aditya23043/split_keyboard/electroholics/2024-12-25_12-39.png

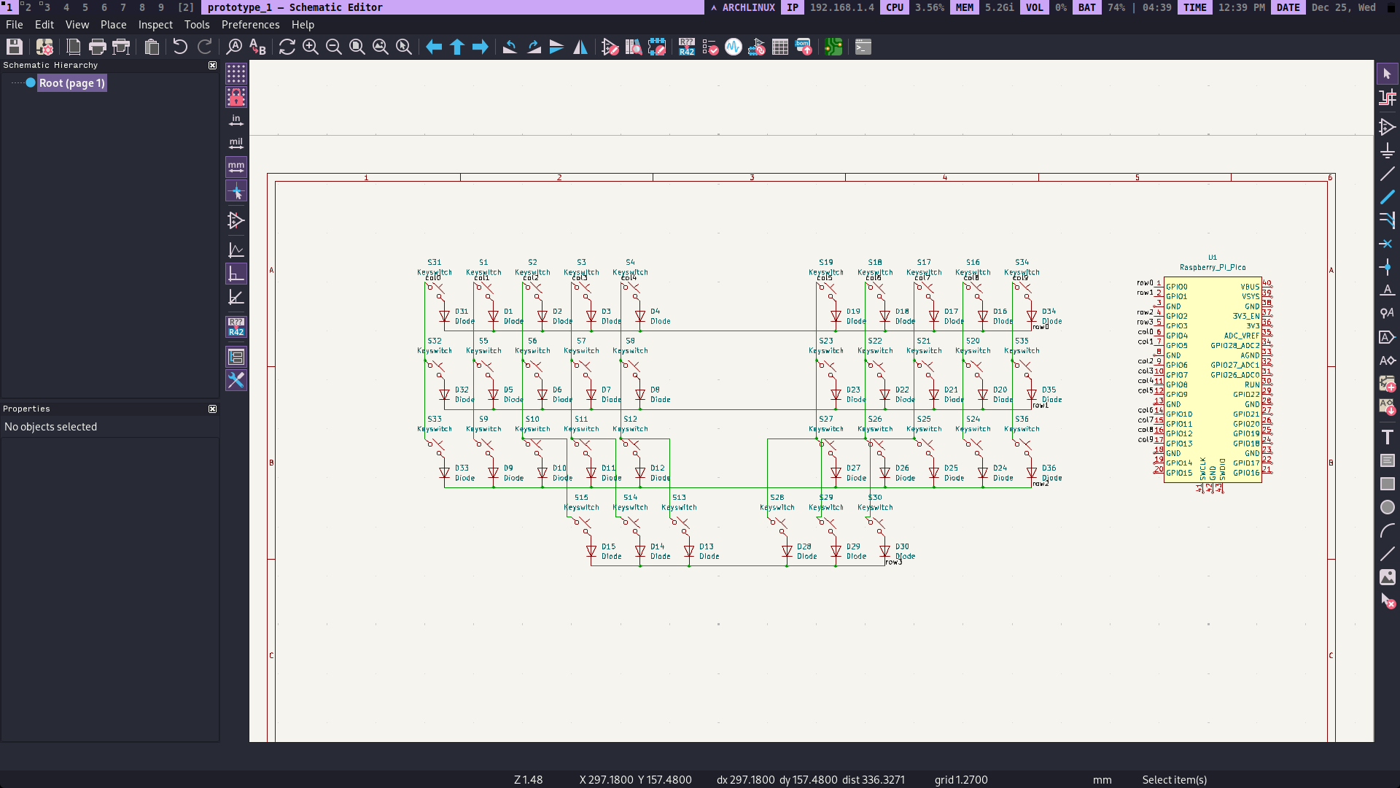
electroholics/2024-12-25_12-39.png
