aditya23043/split_keyboard/imgs/7.jpeg

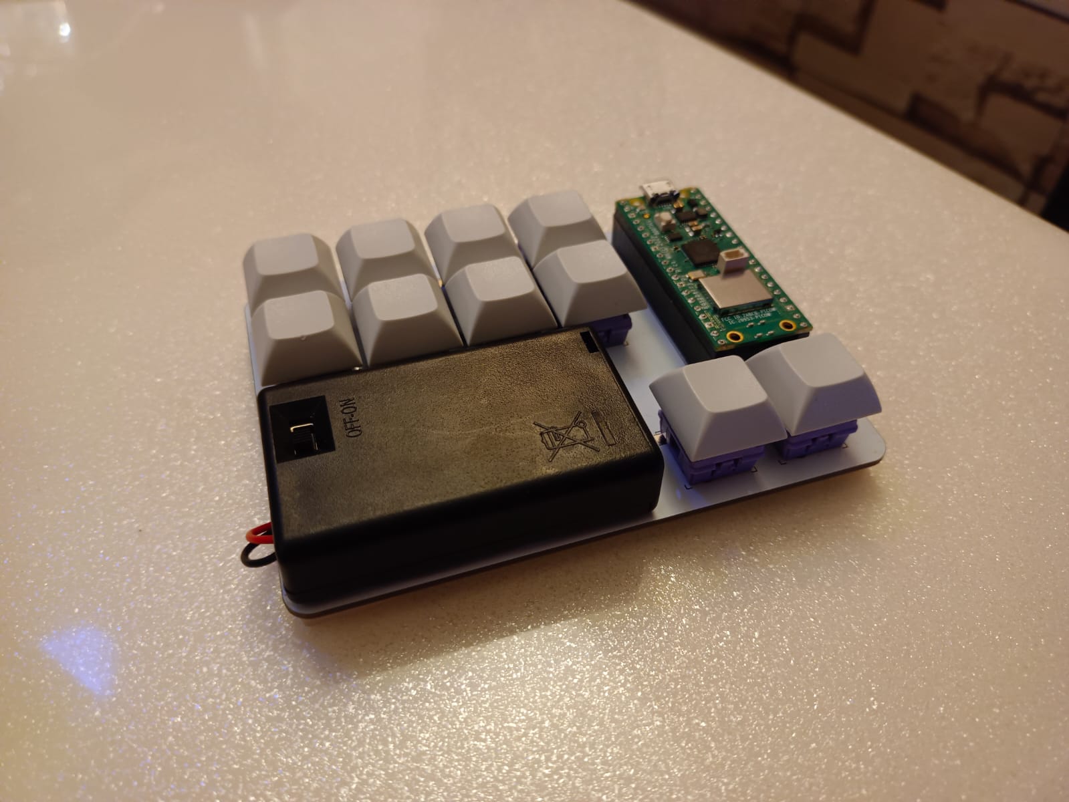
imgs/7.jpeg
