aditya23043/split_keyboard/imgs/8.jpeg

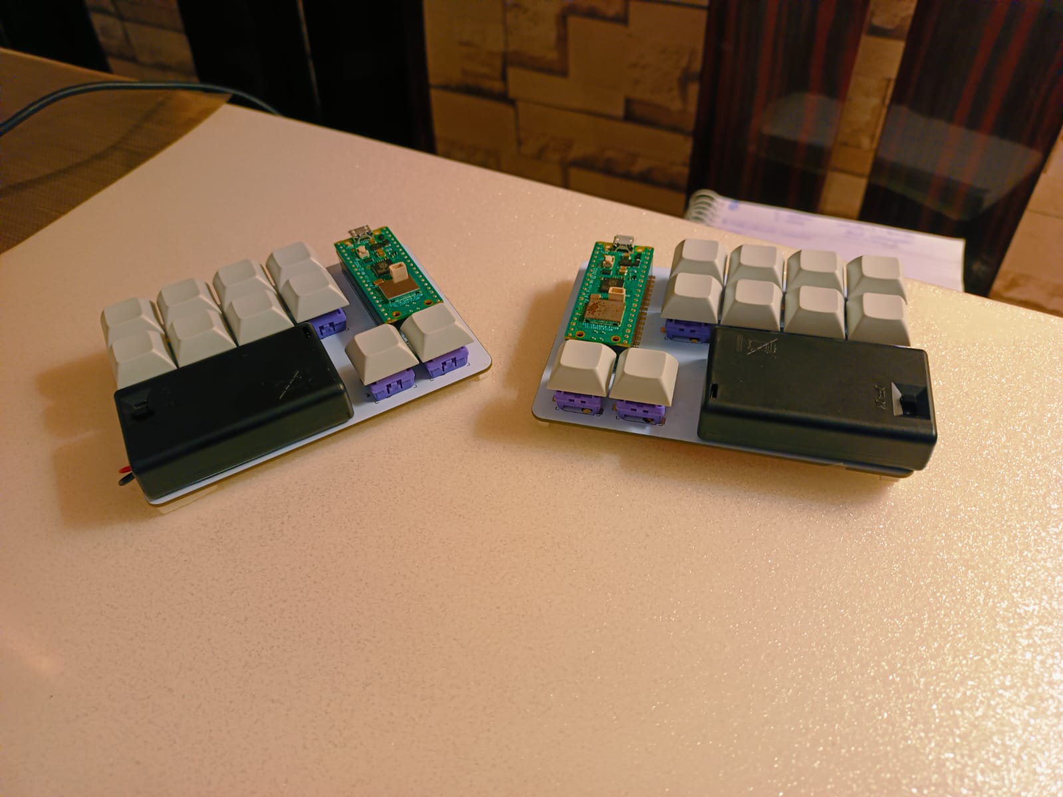
imgs/8.jpeg
