aditya23043/split_keyboard/imgs/10.jpeg

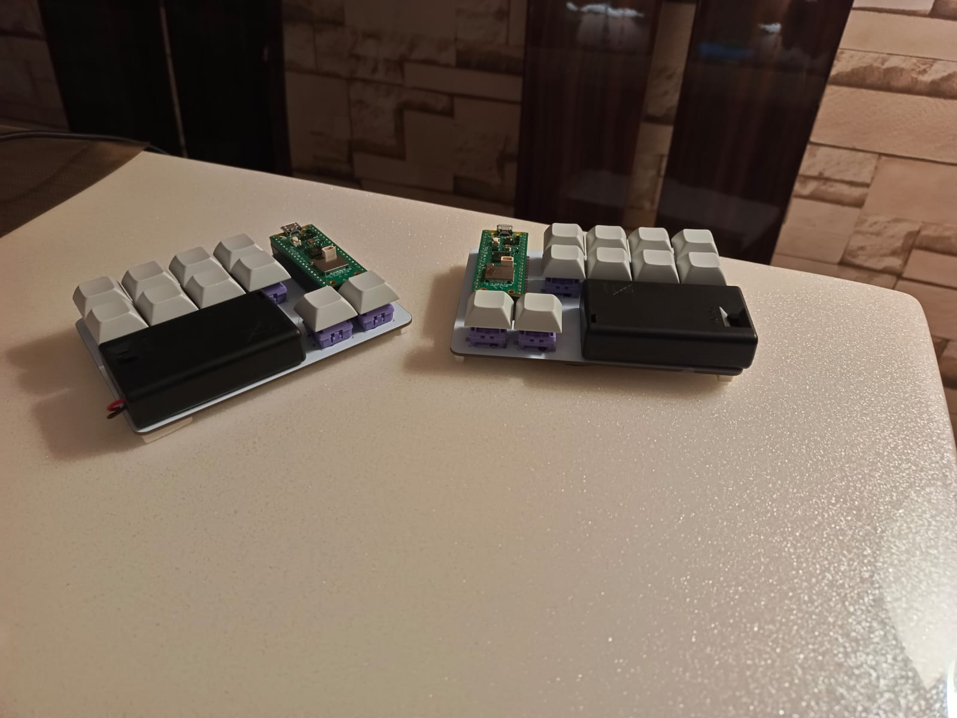
imgs/10.jpeg
