aditya23043/split_keyboard/imgs/13.jpeg

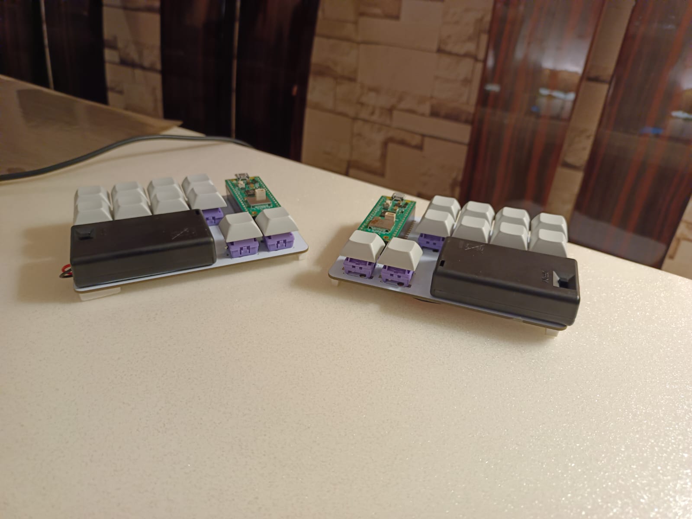
imgs/13.jpeg
