aditya23043/split_keyboard/imgs/22.jpeg

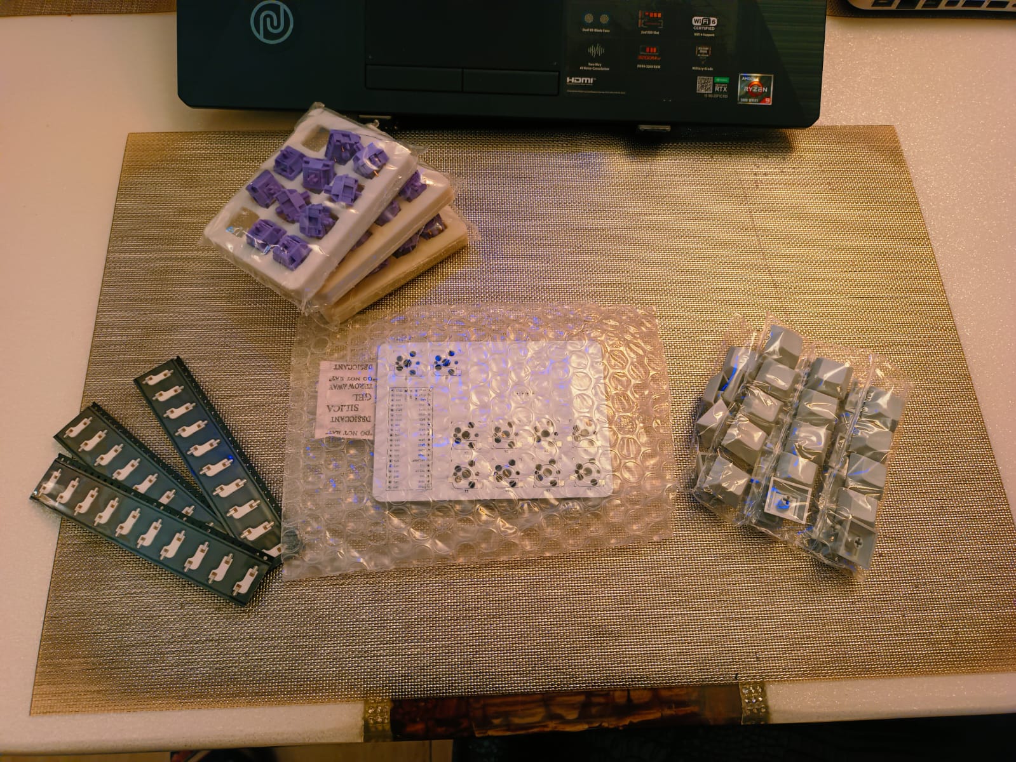
imgs/22.jpeg
