aditya23043/split_keyboard/imgs/2024-10-22_10-09.png

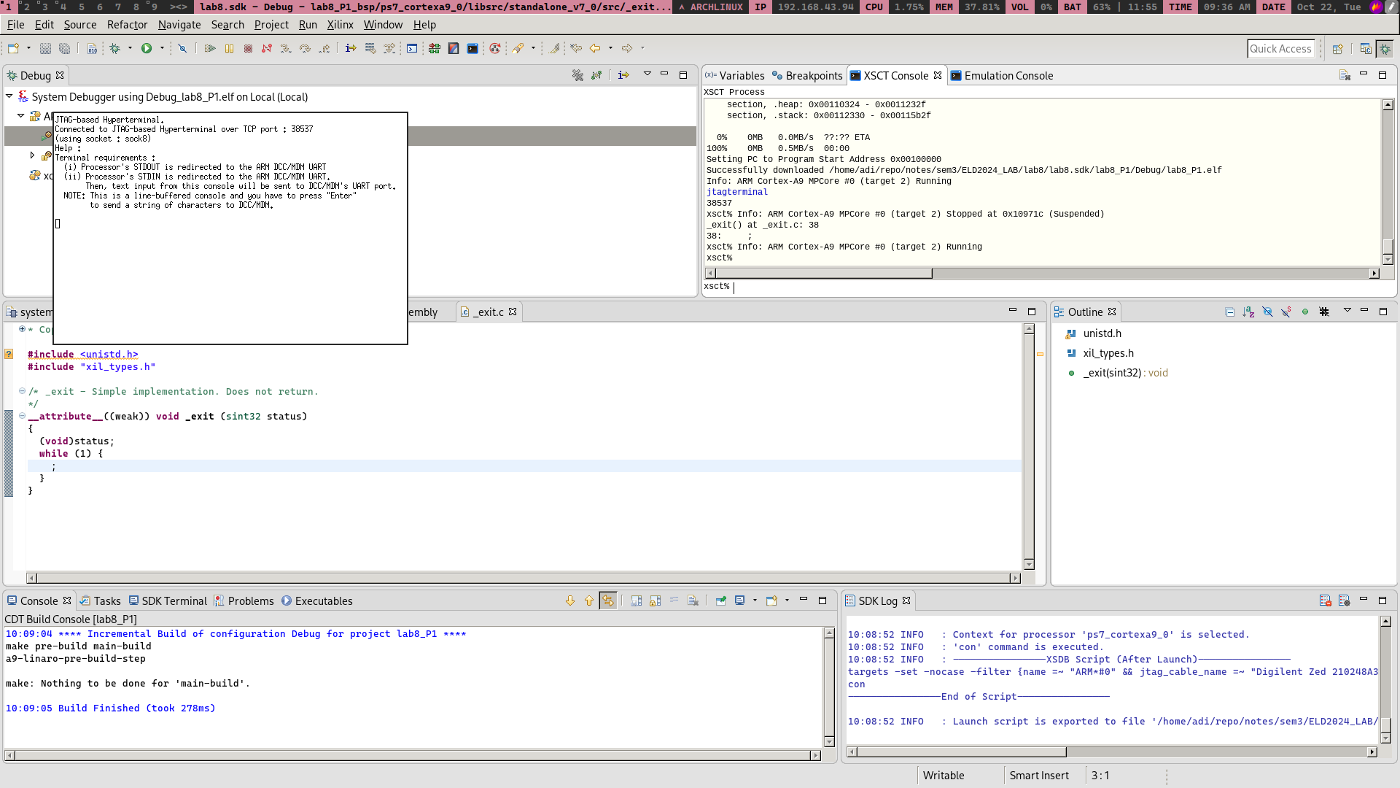
imgs/2024-10-22_10-09.png
